JOKUE2002/Homecockpit/hardware/AP1 - PINMAPPING.png

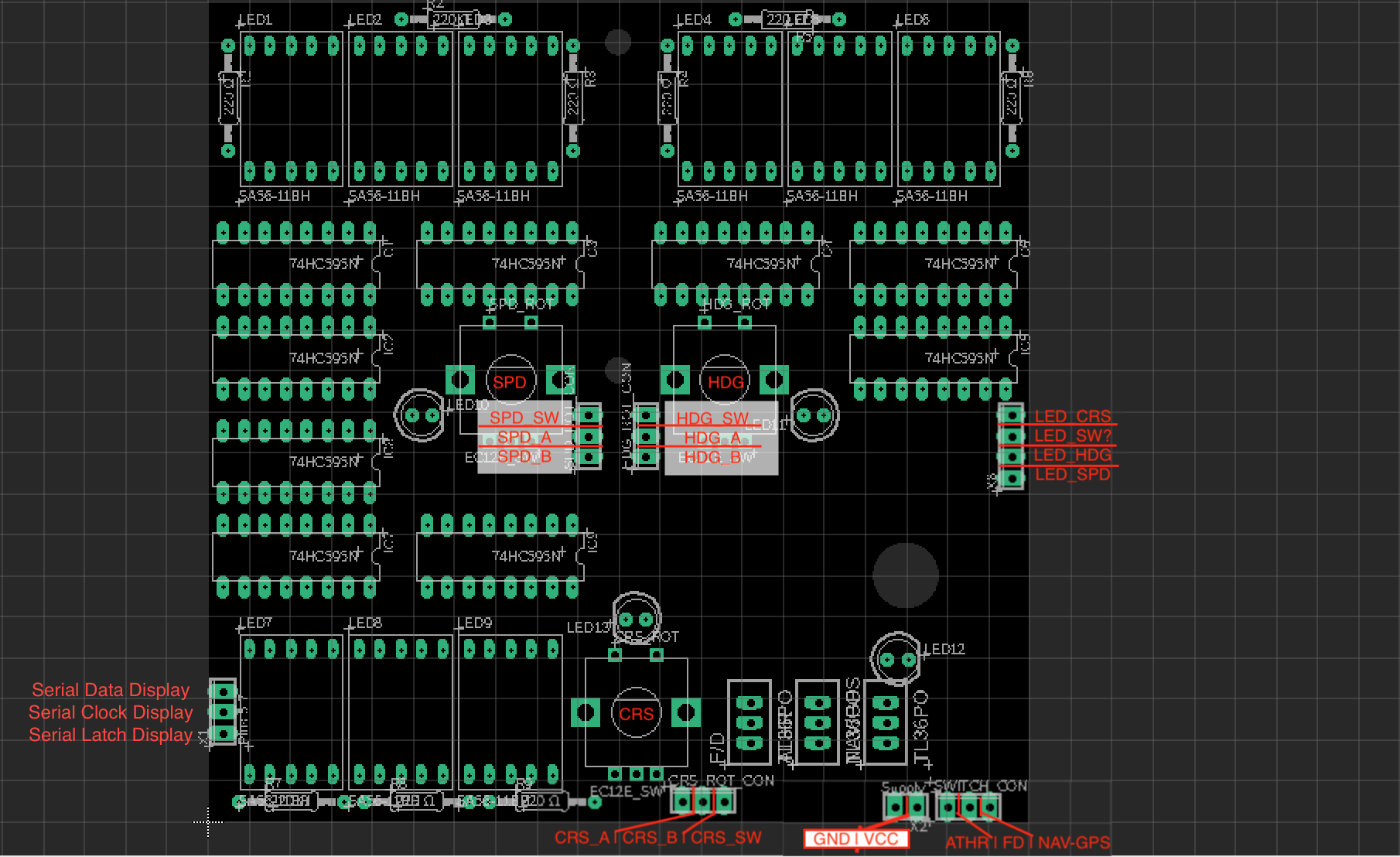
hardware/AP1 - PINMAPPING.png
