JOKUE2002/Homecockpit/hardware/AP2 - PINMAPPING.png

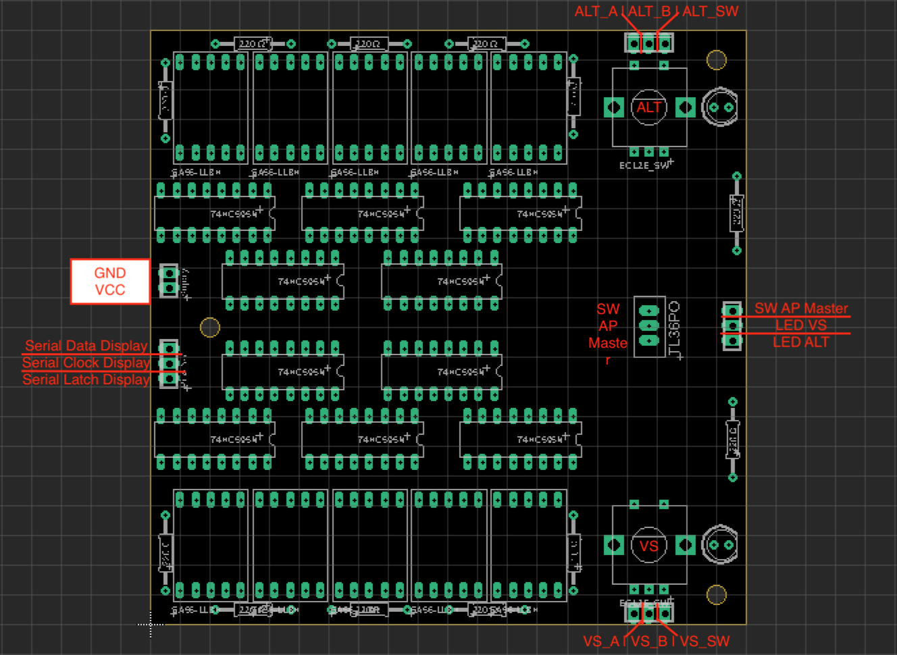
hardware/AP2 - PINMAPPING.png
