JOKUE2002/Homecockpit/hardware/Screenshot_0.png

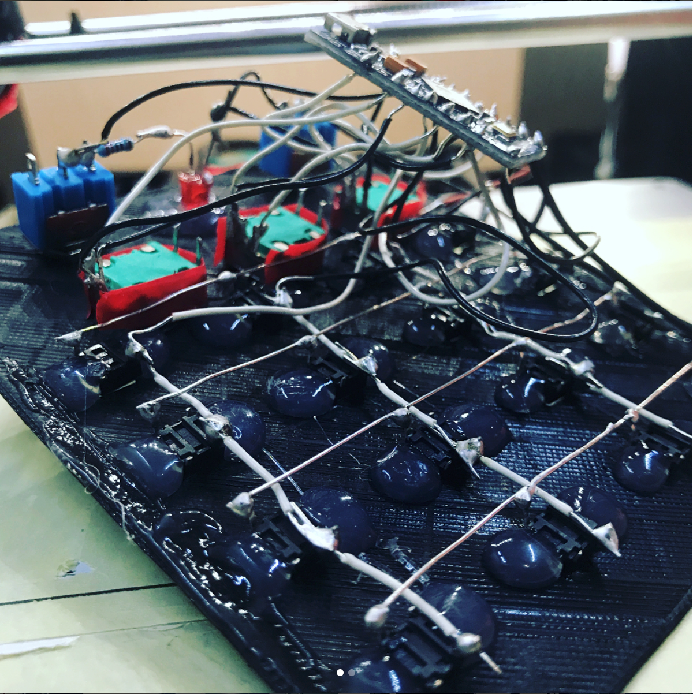
hardware/Screenshot_0.png
