JOKUE2002/Homecockpit/hardware/Screenshot_5.png

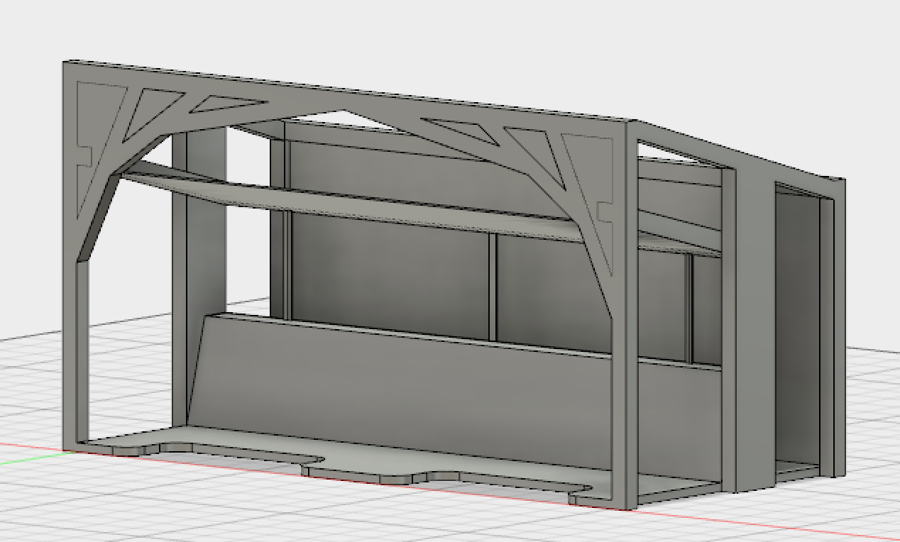
hardware/Screenshot_5.png
