JOKUE2002/Homecockpit/hardware/Screenshot_6.png

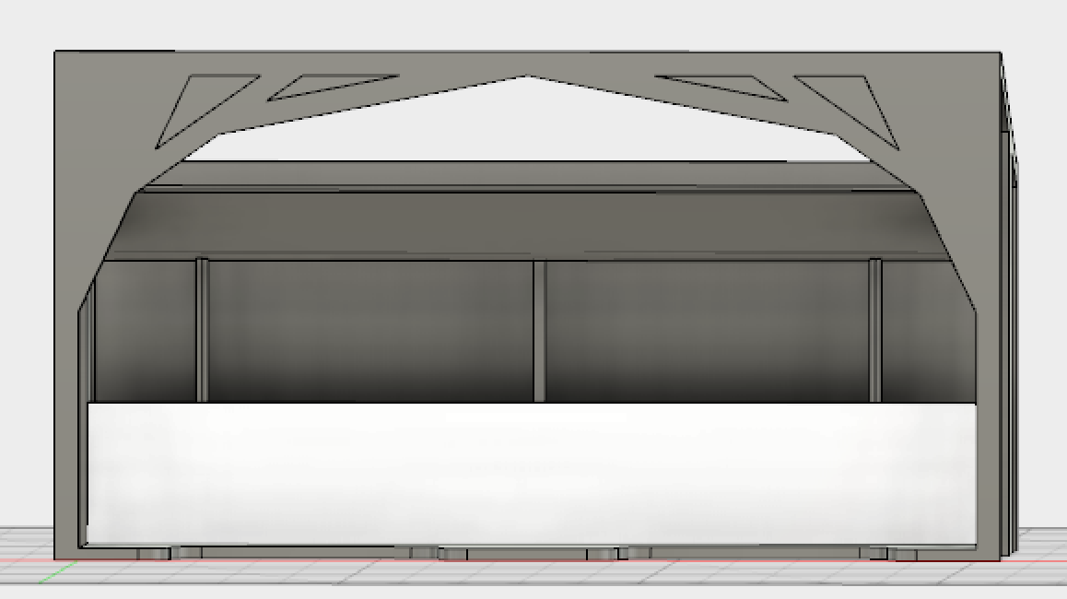
hardware/Screenshot_6.png
