JOKUE2002/Homecockpit/hardware/Screenshot_7.png

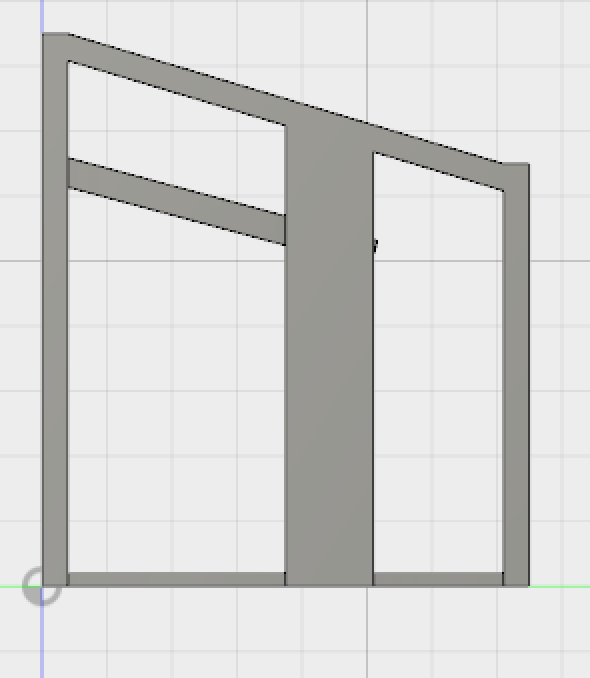
hardware/Screenshot_7.png
