JOKUE2002/Homecockpit/hardware/Screenshot_8.png

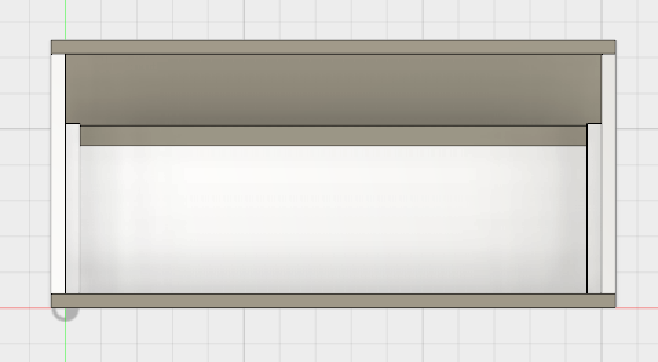
hardware/Screenshot_8.png
