JOKUE2002/Homecockpit/hardware/Screenshot_9.png

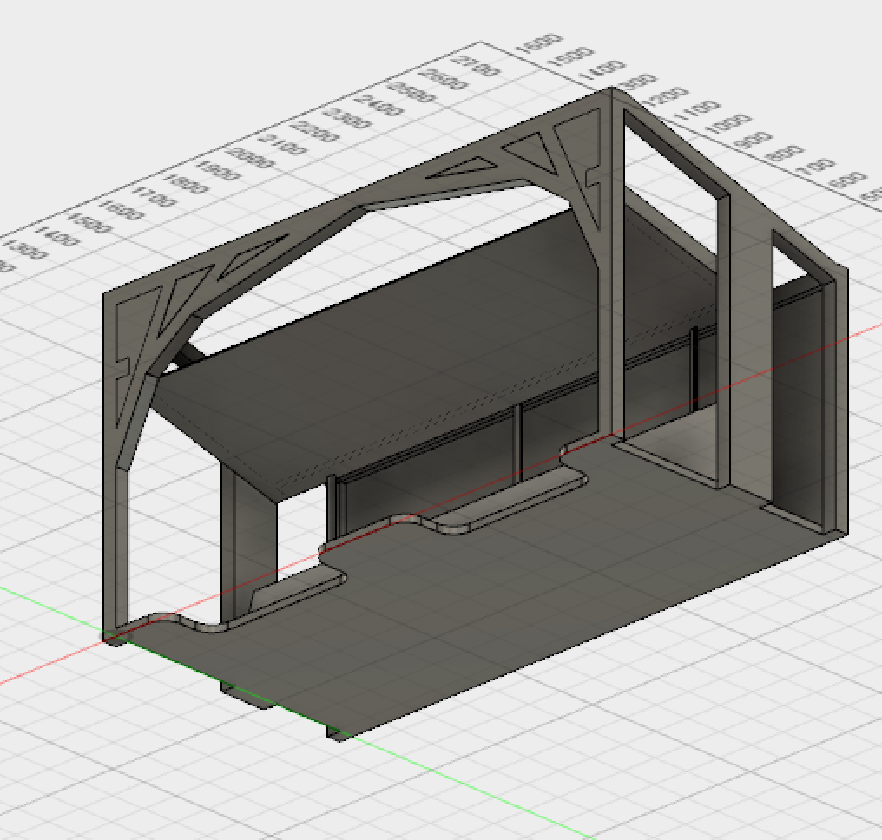
hardware/Screenshot_9.png
